aggerritsen/T-SIMGroveShield/doc/Grove_shield_for_XIAO.png

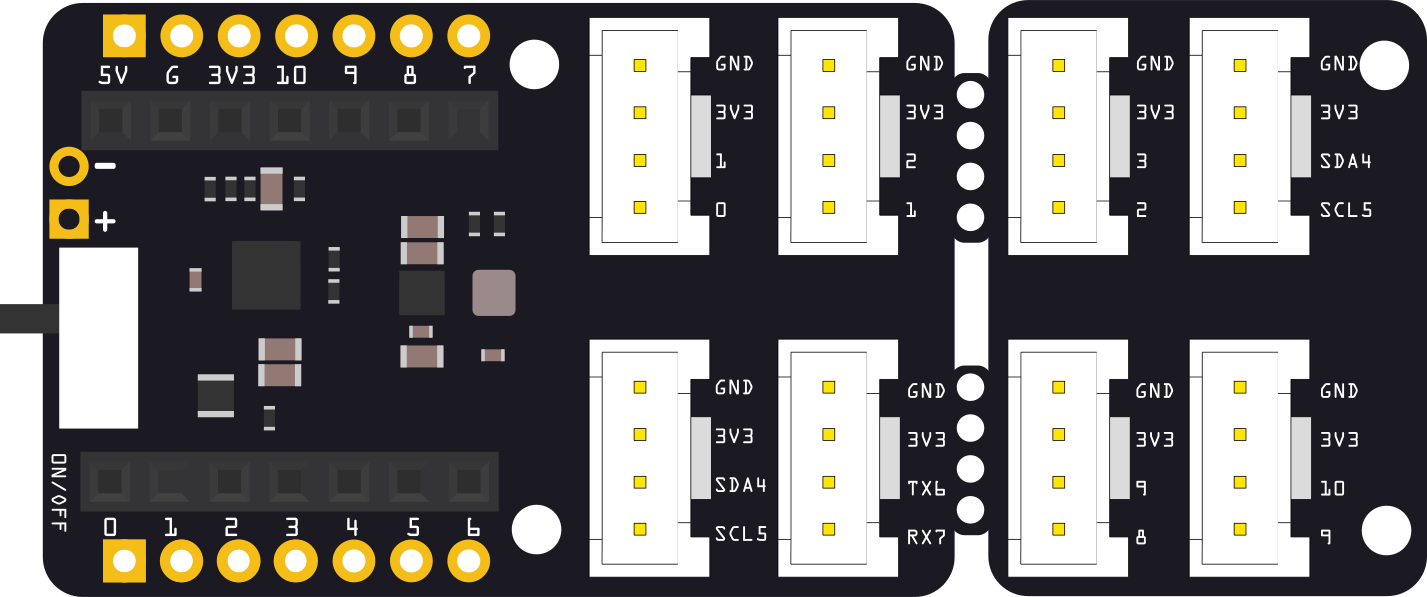
doc/Grove_shield_for_XIAO.png
