aggerritsen/T-SIMGroveShield/pcb/Dual-Vision-Grove-Shield Rev B._etch_silk_bottom.pdf

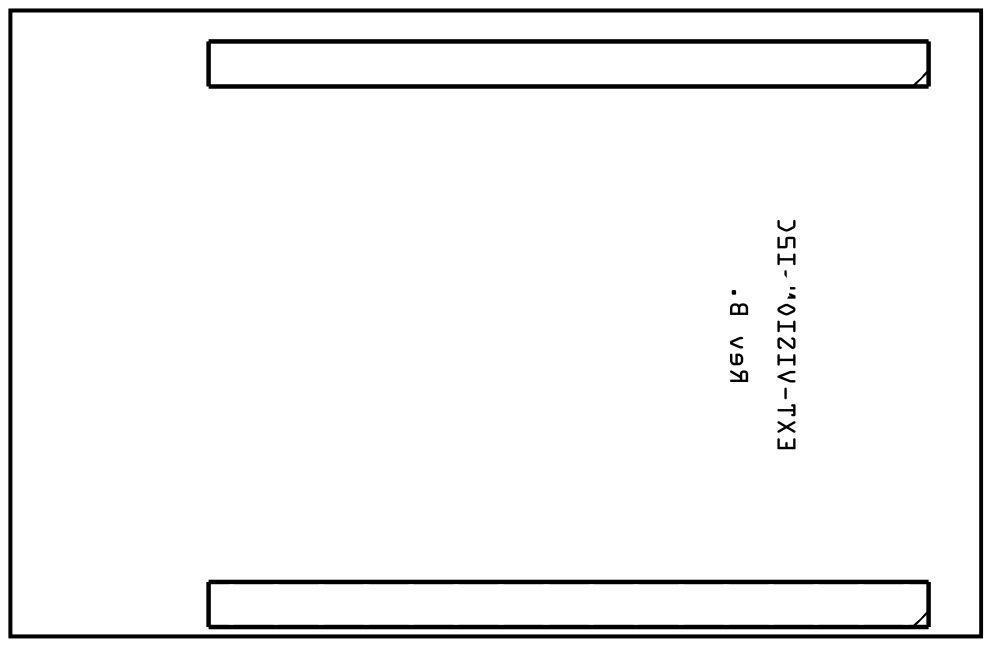
[picture p14: page 1]
