aggerritsen/T-SIMGroveShield/pcb/Dual-Vision-Grove-Shield Rev B._etch_silk_bottom_mirror.pdf

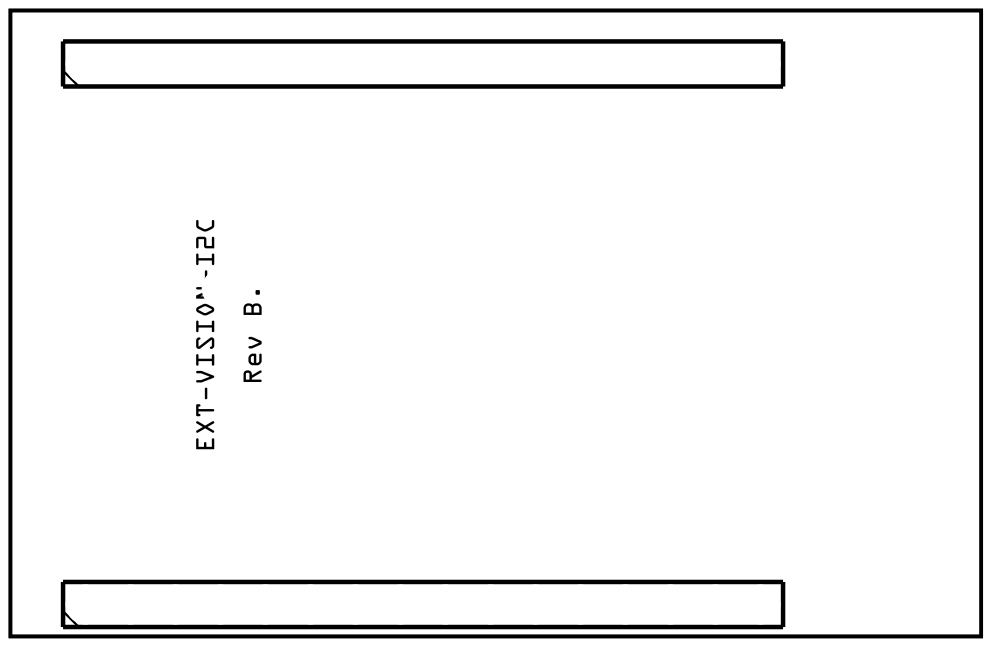
[picture p15: page 1]
