aggerritsen/T-SIMGroveShield/pcb/Dual-Vision-Grove-Shield Rev B._etch_silk_top.pdf

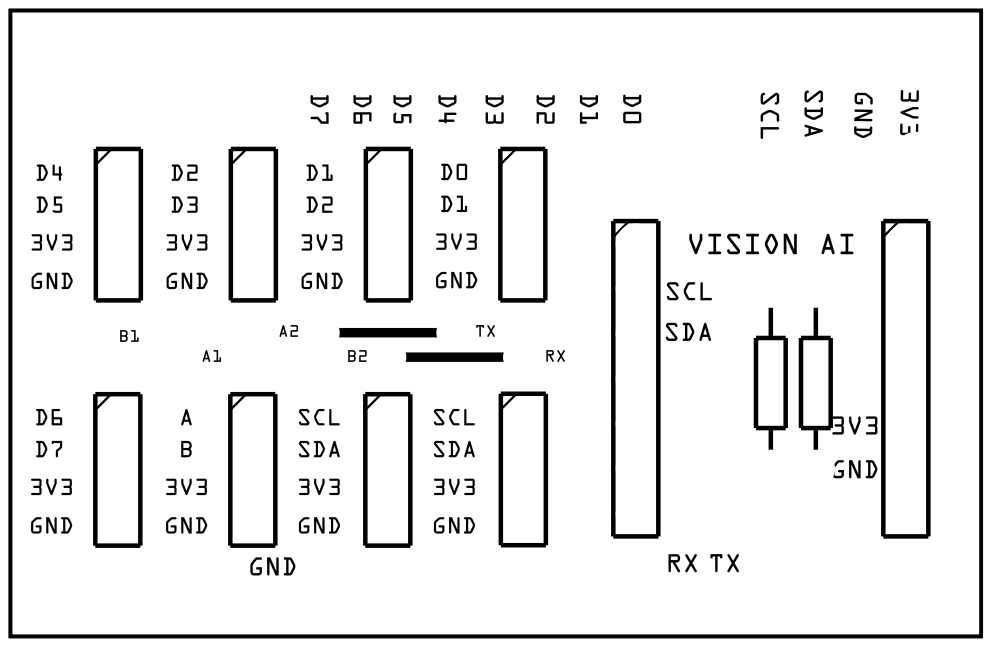
[picture p16: page 1]
