aggerritsen/T-SIMGroveShield/pcb/Dual-Vision-Grove-Shield Rev B._etch_silk_top_mirror.pdf

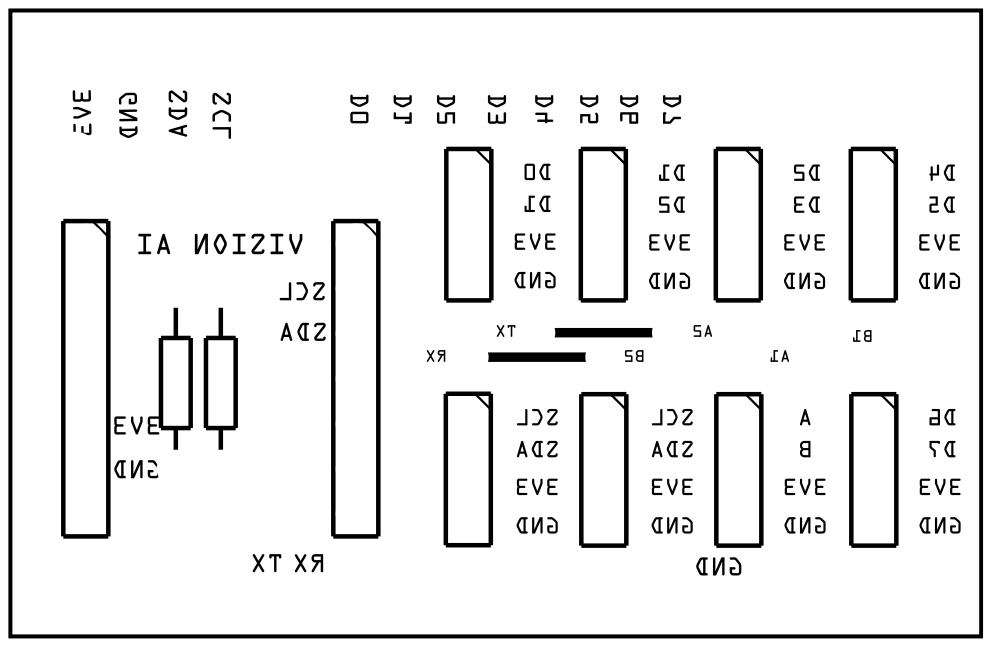
[picture p17: page 1]
